voronov-nikita/arm/scheme/2.jpg

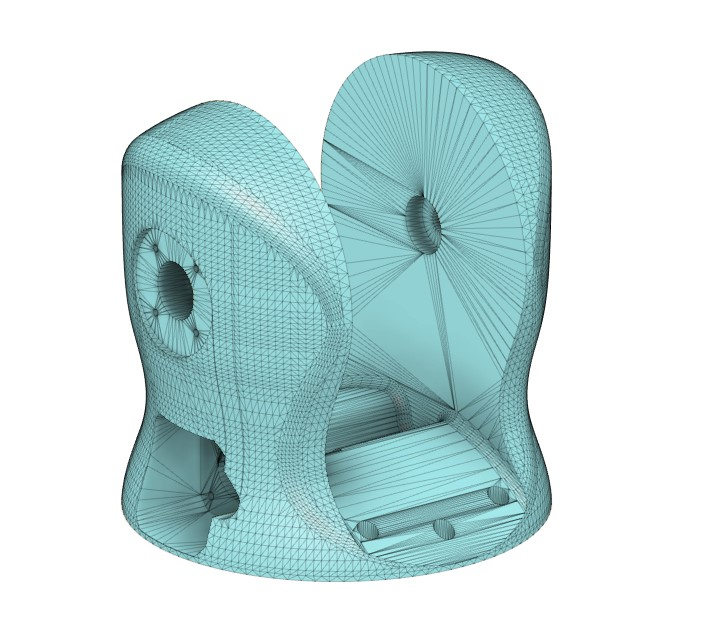
scheme/2.jpg
