voronov-nikita/arm/scheme/3.jpg

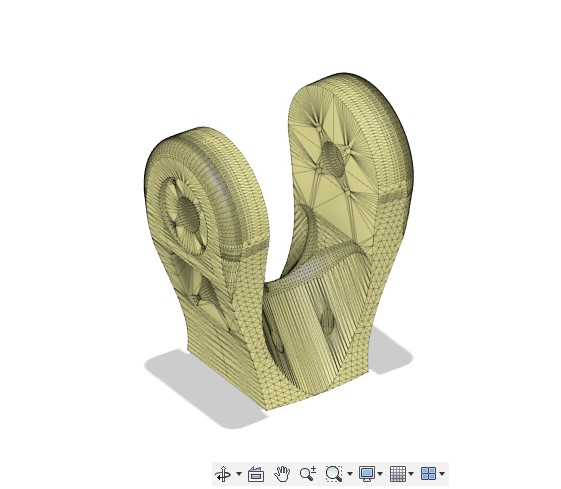
scheme/3.jpg
