voronov-nikita/arm/scheme/6.jpg

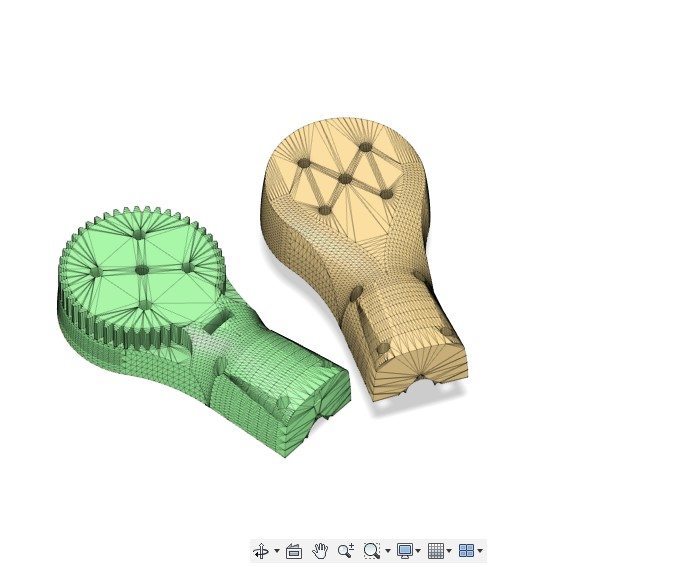
scheme/6.jpg
